gotenham/infraredHorizonSensor/_doc/images/pitch_roll_gimbal_assembly.jpg

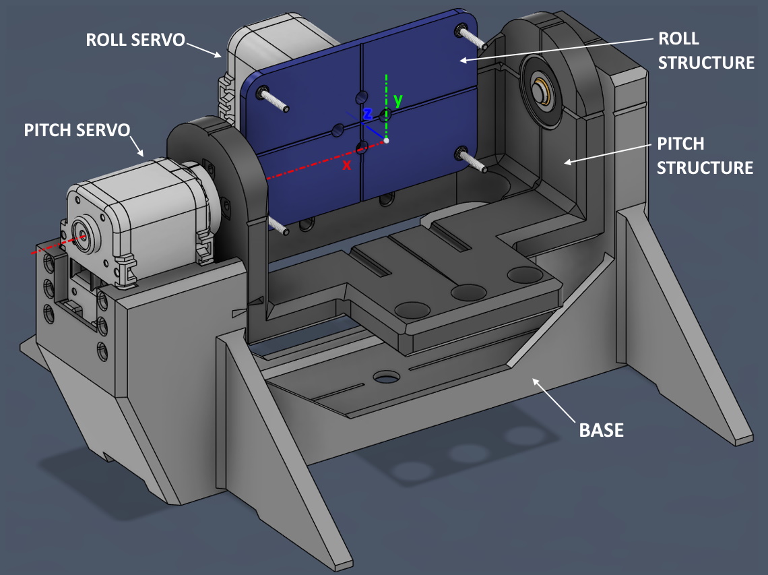
_doc/images/pitch_roll_gimbal_assembly.jpg
