gotenham/infraredHorizonSensor/_doc/images/proxy_orbital_view_test_stand.jpg

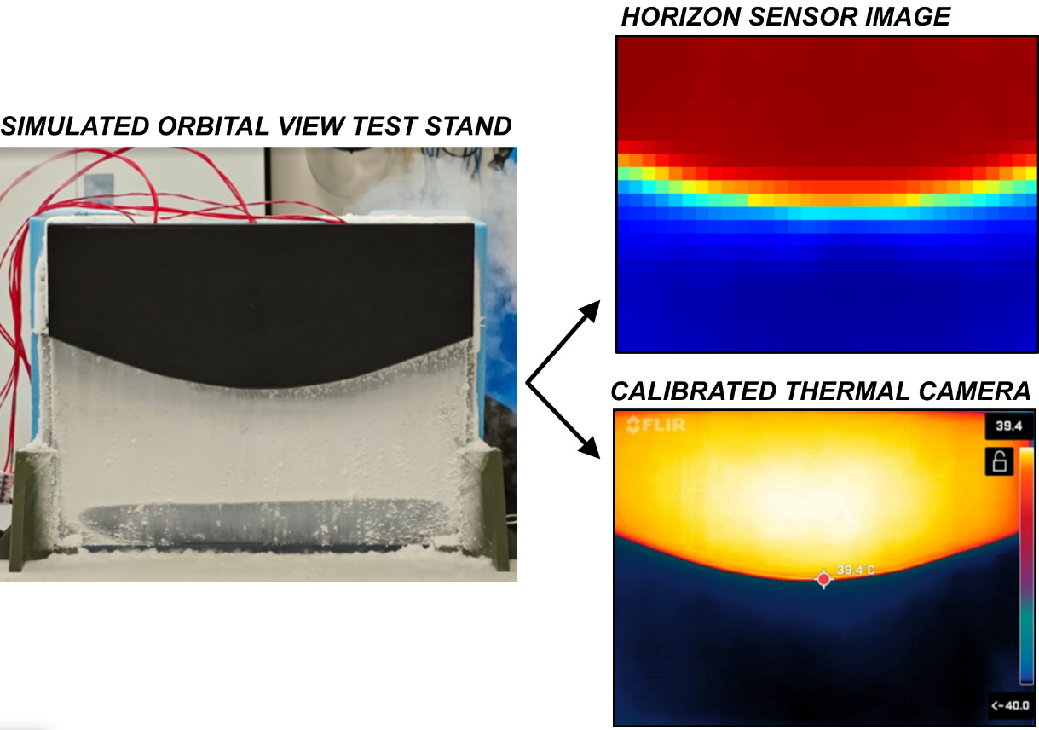
_doc/images/proxy_orbital_view_test_stand.jpg
