gotenham/infraredHorizonSensor/device_firmware/Src/mtxCV.cpp

/*
 * mtxCV.cpp
 *
 *  Created on: Apr 7, 2024
 *      Author: AJ
 */

/* printf REFERENCE:
    %c	character
    %d	decimal (integer) number (base 10)
    %e	exponential floating-point number
    %f	floating-point number
    %i	integer (base 10)
    %o	octal number (base 8)
    %s	a string of characters
    %u	unsigned decimal (integer) number
    %x	number in hexadecimal (base 16)
    %%	print a percent sign
    \%	print a percent sign
NOTE on ImageType template:
template<typename MatrixType>
void exampleFunction(MatrixType& image) {
    //Cast to type associated with MatrixType:
    image(jRow, iCol) = static_cast<typename MatrixType::Scalar>(xyz);

    //Cast MatrixType element to type
    float varFloat = static_cast<float>(image(jRow, iCol));

    //Cast entire image matrix to type
    MatrixXf mtxFloat = image.template cast<float>();

    //convert data type without copying the matrix using map (changes to one matrix are reflected in the other)
    MatrixXf mappedImage(image.rows(), image.cols());
    mappedImage = Map<MatrixXf>(image.data(), image.rows(), image.cols());

// Checking MatrixType data type and structure
    <<Specific DataType>> if constexpr(std::is_same<typename MatrixType::Scalar, float>::value) {} //see std template: is_same<T, T>:std::true_type {};
    <<float, double etc>> if constexpr(std::is_floating_point<typename MatrixType::Scalar>::value) {}
    <<all signed and unsigned integer types>> if constexpr(std::is_integral<typename MatrixType::Scalar>::value) {}
    <<all signed integer types>> if constexpr(std::is_signed<typename MatrixType::Scalar>::value) {}
    <<all unsigned integer types>> if constexpr(std::is_unsigned<typename MatrixType::Scalar>::value) {}
    <<type is Matrix>> if constexpr(Eigen::is_matrix<MatrixType>::value) {}
    <<type is Array>> if constexpr(Eigen::is_array<MatrixType>::value) {}
    <<type is Vector>> if constexpr(Eigen::is_vector<MatrixType>::value) {}

 Use constexpr variable declaration to flag value to be computed at compile time.
}

+++++++++++++ EXAMPLE IMG ROTATIONS +++++++++++++ //
    //FLIP VERTICAL
    thermalImg.rowwise().reverseInPlace();

    //FLIP HORIZONTAL
    thermalImg.colwise().reverseInPlace();

    //ROTATE CCW 90 degrees
    thermalImg.transposeInPlace();
    thermalImg.colwise().reverseInPlace();

    //ROTATE CW 90 degrees
    thermalImg.transposeInPlace();
    thermalImg.rowwise().reverseInPlace();
+++++++++++++ NEXT SECTION +++++++++++++ //
*/
	#include "mtxCV.h"

	// Example data structure for MLX90640 sensor image output for testing
//	const float thermalImageArr[768] = {0.497f, 0.f, 0.1f, 0.1f, 0.f, 0.f, 0.f, 0.f, 0.f, 0.f, 0.f, 0.f, 0.f, 0.f, 0.f, 0.f, 0.f, 0.f, 0.f, 0.f, 0.f, 0.f, 0.f, 0.f, 0.f, 0.f, 0.f, 0.f, 0.f, 0.f, 0.f, 0.f,
//	0.f, 0.f, 0.f, 0.f, 0.f, 0.f, 0.f, 0.f, 0.f, 6.497f, 0.f, 0.f, 0.f, 0.f, 0.f, 0.f, 0.f, 0.f, 0.f, 0.f, 1.624f, 0.f, 0.f, 6.497f, 0.f, 0.f, 0.f, 1.624f, 0.f, 0.f, 0.f, 0.f,
//	1.624f, 0.f, 0.f, 0.f, 0.f, 0.f, 0.f, 0.f, 1.624f, 0.f, 0.f, 0.f, 1.624f, 0.f, 0.f, 0.f, 0.f, 0.f, 0.f, 0.f, 0.f, 0.f, 0.f, 0.f, 0.f, 0.f, 0.f, 0.f, 0.f, 0.f, 6.497f, 0.f,
//	0.f, 1.624f, 0.f, 0.f, 0.f, 0.f, 0.f, 0.f, 0.f, 0.f, 0.f, 0.f, 0.f, 6.497f, 0.f, 0.f, 0.f, 0.f, 0.f, 0.f, 0.f, 0.f, 0.f, 1.624f, 0.f, 0.f, 0.f, 0.f, 0.f, 0.f, 0.f, 0.f,
//	0.f, 6.497f, 0.f, 0.f, 0.f, 0.f, 0.f, 0.f, 0.f, 0.f, 0.f, 0.f, 0.f, 0.f, 0.f, 0.f, 0.f, 0.f, 0.f, 0.f, 0.f, 0.f, 0.f, 0.f, 0.f, 0.f, 0.f, 0.f, 0.f, 0.f, 0.f, 0.f,
//	0.f, 0.f, 0.f, 0.f, 0.f, 6.497f, 0.f, 0.f, 1.624f, 0.f, 0.f, 0.f, 0.f, 0.f, 1.624f, 0.f, 0.f, 0.f, 0.f, 0.f, 0.f, 0.f, 0.f, 0.f, 0.f, 0.f, 6.497f, 0.f, 0.f, 0.f, 0.f, 0.f,
//	0.f, 0.f, 0.f, 0.f, 0.f, 0.f, 0.f, 0.f, 0.f, 0.f, 0.f, 0.f, 0.f, 0.f, 0.f, 0.f, 0.f, 0.f, 0.f, 0.f, 0.f, 0.f, 0.f, 0.f, 0.f, 0.f, 0.f, 0.f, 0.f, 0.f, 0.f, 0.f,
//	0.f, 0.f, 0.f, 0.f, 0.f, 0.f, 0.f, 0.f, 0.f, 0.f, 0.f, 0.f, 0.f, 0.f, 0.f, 0.f, 0.f, 0.f, 0.f, 0.f, 0.f, 0.f, 0.f, 0.f, 0.f, 0.f, 0.f, 0.f, 0.f, 0.f, 0.f, 0.f,
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
//	6.497f, 6.497f, 4.873f, 4.873f, 4.873f, 4.873f, 6.497f, 6.497f, 8.121f, 8.121f, 11.369f, 11.369f, 9.745f, 9.745f, 8.121f, 8.121f, 6.497f, 6.497f, 6.497f, 6.497f, 3.248f, 3.248f, 3.248f, 3.248f, 4.873f, 4.873f, 3.248f, 3.248f, 1.624f, 1.624f, 0.f, 0.f,
//	6.497f, 6.497f, 4.873f, 4.873f, 4.873f, 4.873f, 6.497f, 6.497f, 8.121f, 8.121f, 11.369f, 11.369f, 9.745f, 9.745f, 8.121f, 8.121f, 6.497f, 6.497f, 6.497f, 6.497f, 3.248f, 3.248f, 3.248f, 3.248f, 4.873f, 4.873f, 3.248f, 3.248f, 1.624f, 1.624f, 0.f, 0.f};
